CedricB-hub/PCB-Layout/Design Files/V1I1/3d models/Regulator_TPS73701DCQ.step

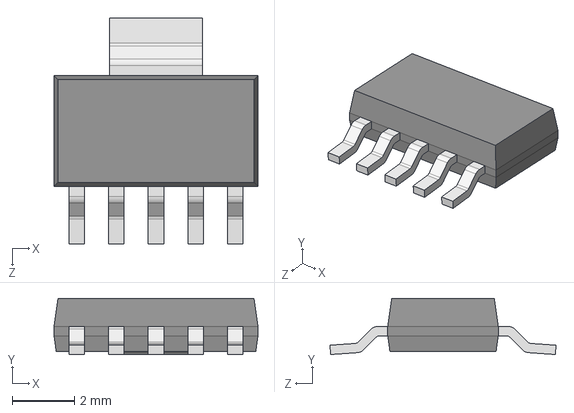
[picture p15: CAD file, 2020-06-24]
Design Files/V1I1/3d models/Regulator_TPS73701DCQ.step
6.55 x 1.80 x 7.26 mm
