CedricB-hub/PCB-Layout/Design Files/V1I1/3d models/dil_socket.stp

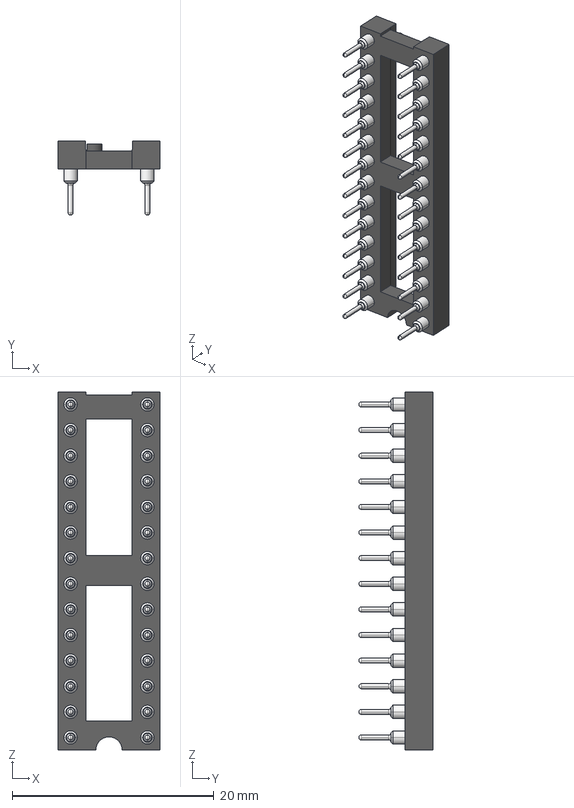
[picture p16: CAD file, 2020-06-24]
Design Files/V1I1/3d models/dil_socket.stp
10.1 x 7.37 x 35.5 mm
