CedricB-hub/PCB-Layout/Design Files/V1I1/3d models/m20-7820646_asm.stp

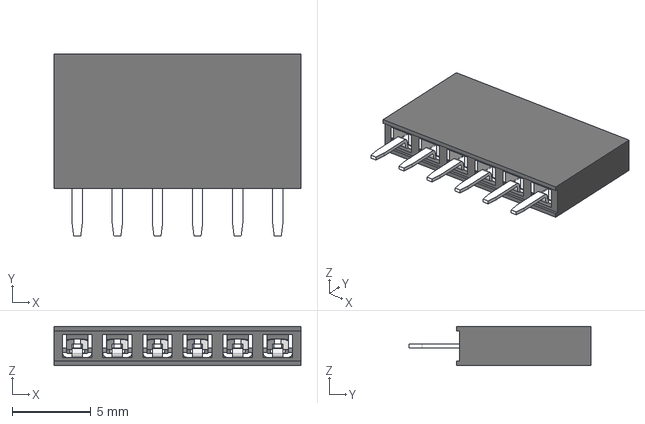
[picture p17: CAD file, 2020-06-24]
Design Files/V1I1/3d models/m20-7820646_asm.stp
15.6 x 11.5 x 2.50 mm
M20-78206_MOULD
M20-782_CONTACT x 6
