CedricB-hub/PCB-Layout/Design Files/V1I1/3d models/m20-7820842_asm.stp

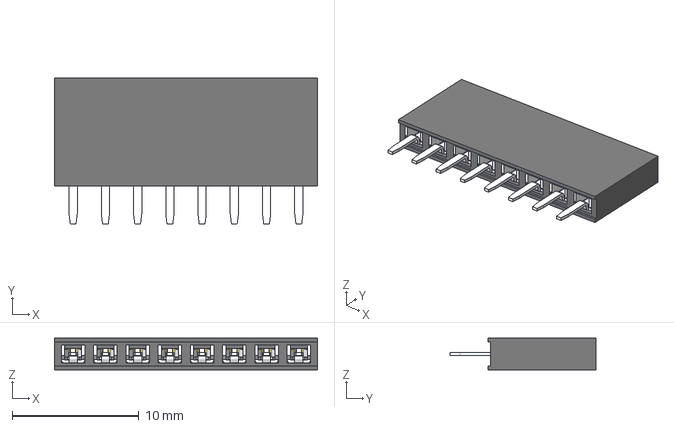
[picture p18: CAD file, 2020-06-24]
Design Files/V1I1/3d models/m20-7820842_asm.stp
20.7 x 11.5 x 2.50 mm
M20-78208_MOULD
M20-782_CONTACT x 8
