CedricB-hub/PCB-Layout/!Released Files/Step 2 - Board Assembly/28PINS - V1I1- Variant 5V/28PINS_Draftsman_5V.PDF

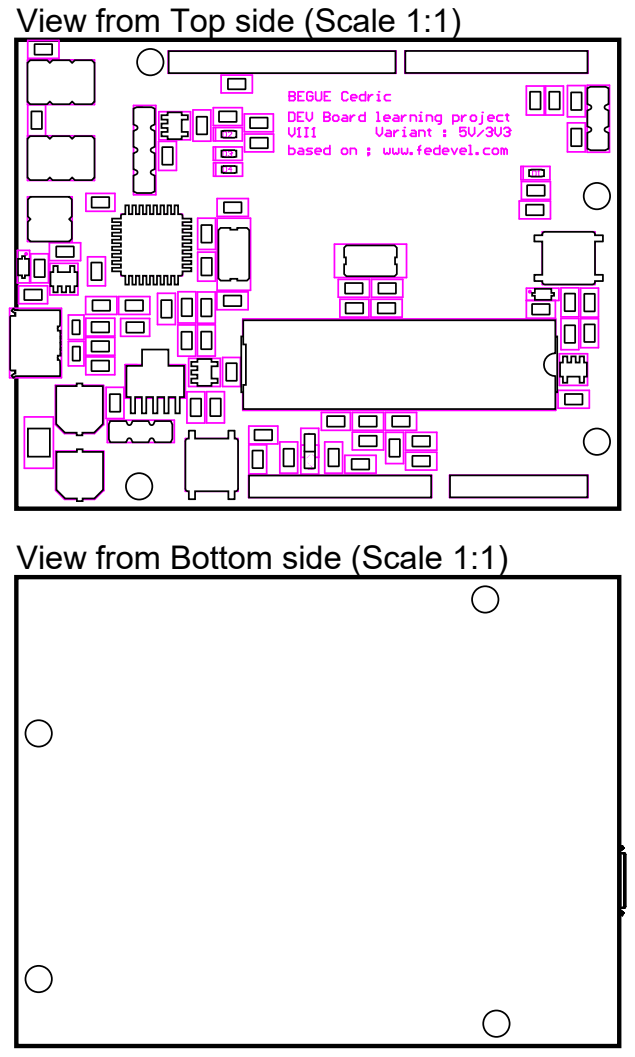
[picture p43: page 1]

View from Top side (Scale 1:1)

View from Bottom side (Scale 1:1)
