CedricB-hub/PCB-Layout/!Released Files/Step 2 - Board Assembly/28PINS - V1I1- Variant 5V/28PINS_TopViewDrawing_5V.PDF

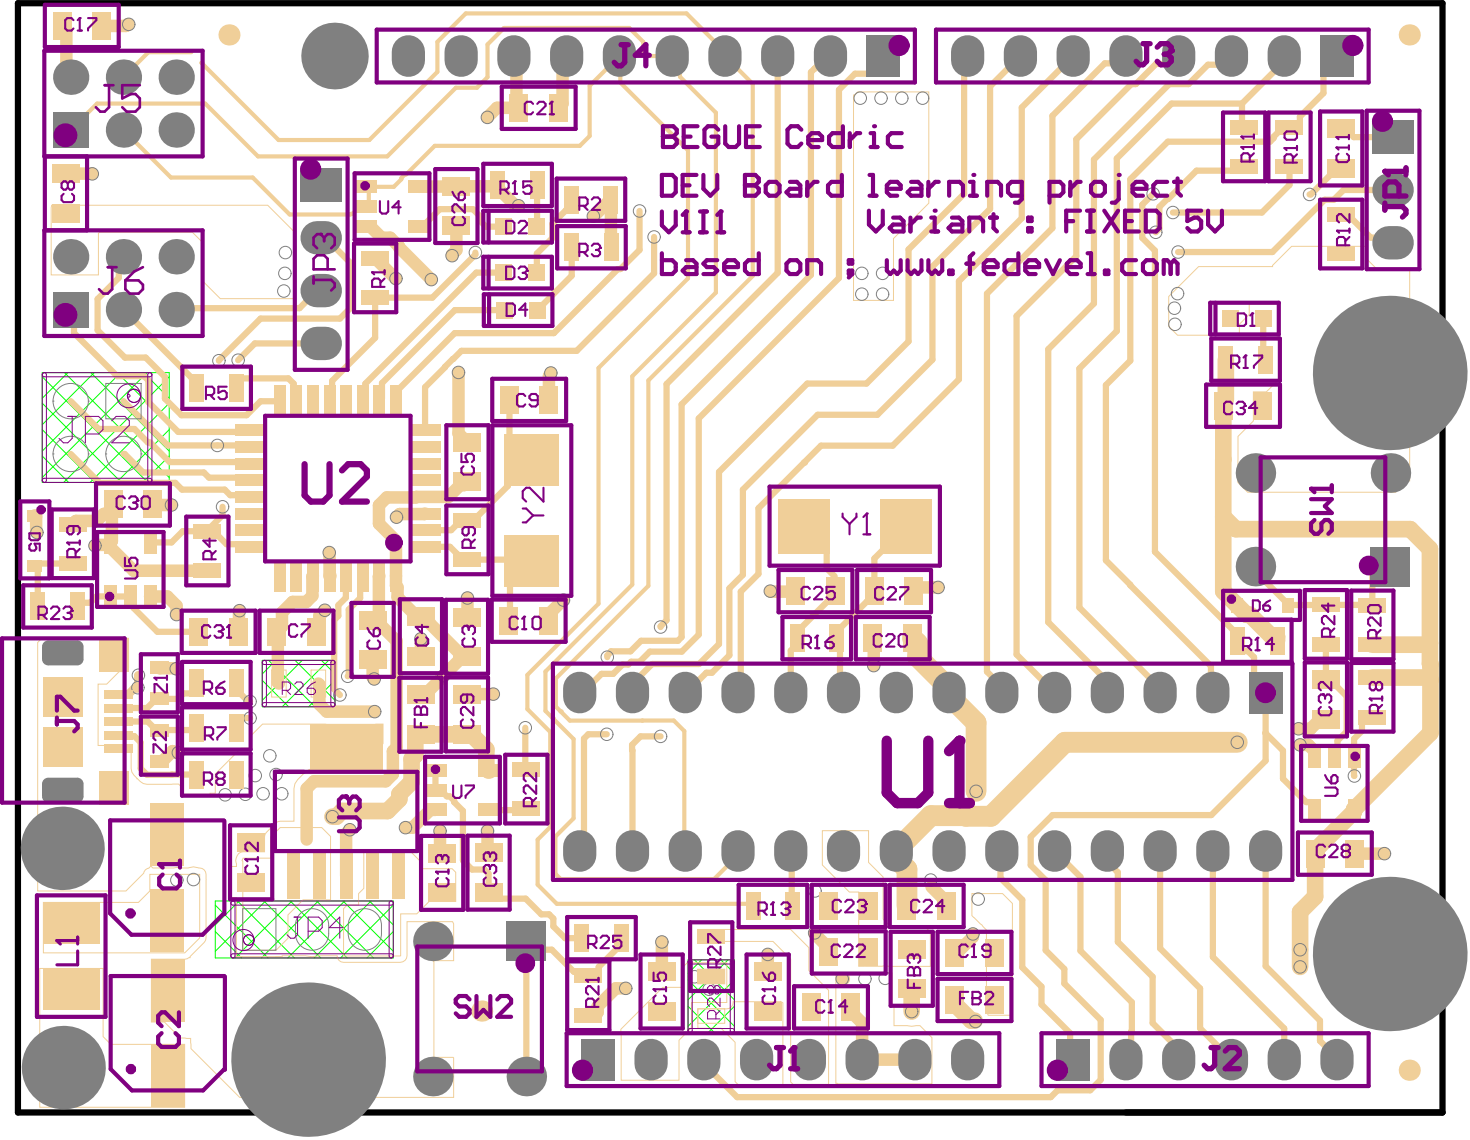
[picture p44: page 1]
